OpenEEC-Project/EECSucka-Archive/Sucka/EEC Sucka/esk_bot2.jpg

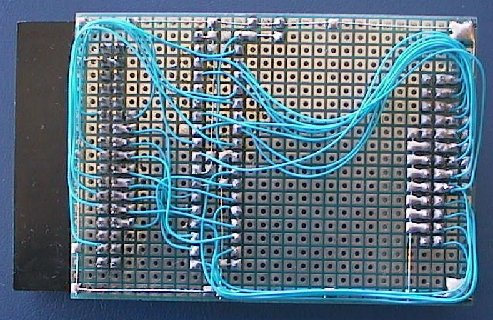
Sucka/EEC Sucka/esk_bot2.jpg
