OpenEEC-Project/EECSucka-Archive/Sucka/EEC Sucka/esk_top2.jpg

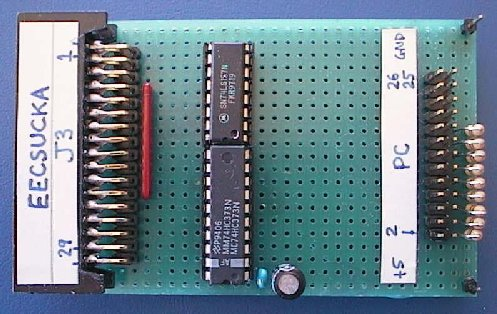
Sucka/EEC Sucka/esk_top2.jpg
