OpenEEC-Project/EECSucka-Archive/Sucka/EZTag/EZTag.bmp

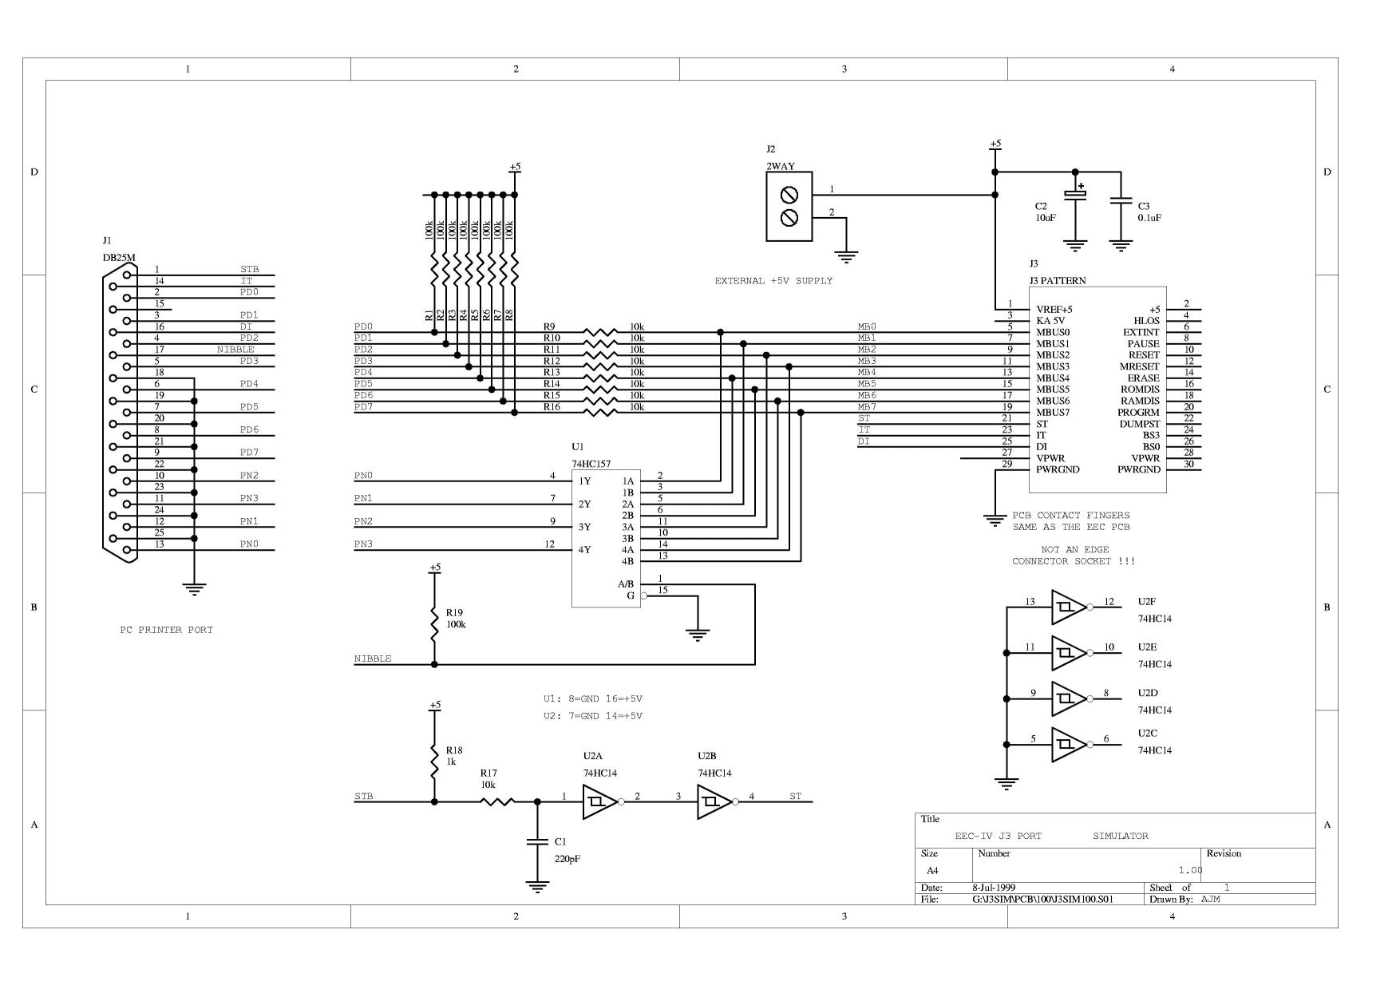
Sucka/EZTag/EZTag.bmp
