OpenEEC-Project/EECSucka-Archive/Sucka/J3 adapter/ea100b_2.jpg

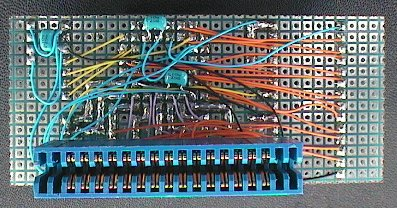
Sucka/J3 adapter/ea100b_2.jpg
