OpenEEC-Project/EECSucka-Archive/Sucka/J3 adapter/ea100w_2.gif

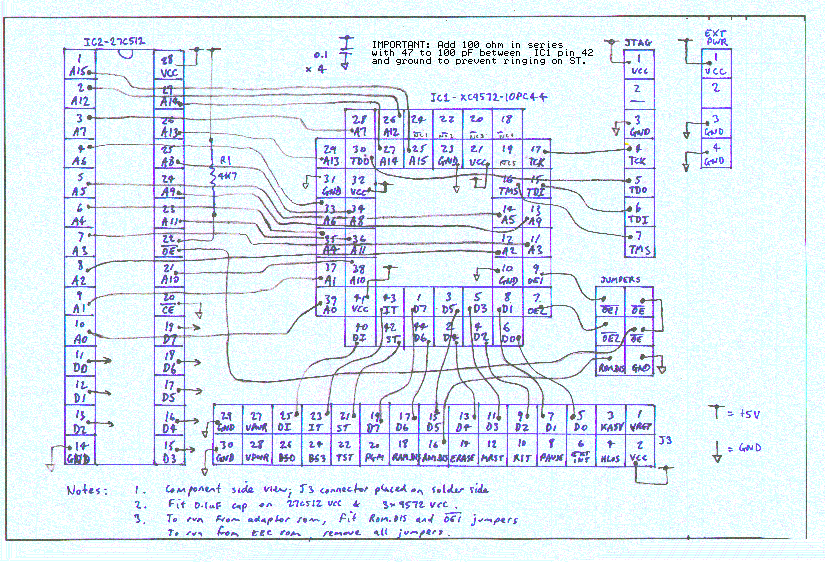
Sucka/J3 adapter/ea100w_2.gif
