OpenEEC-Project/EECSucka-Archive/Sucka/J3 adapter/j3_2.gif

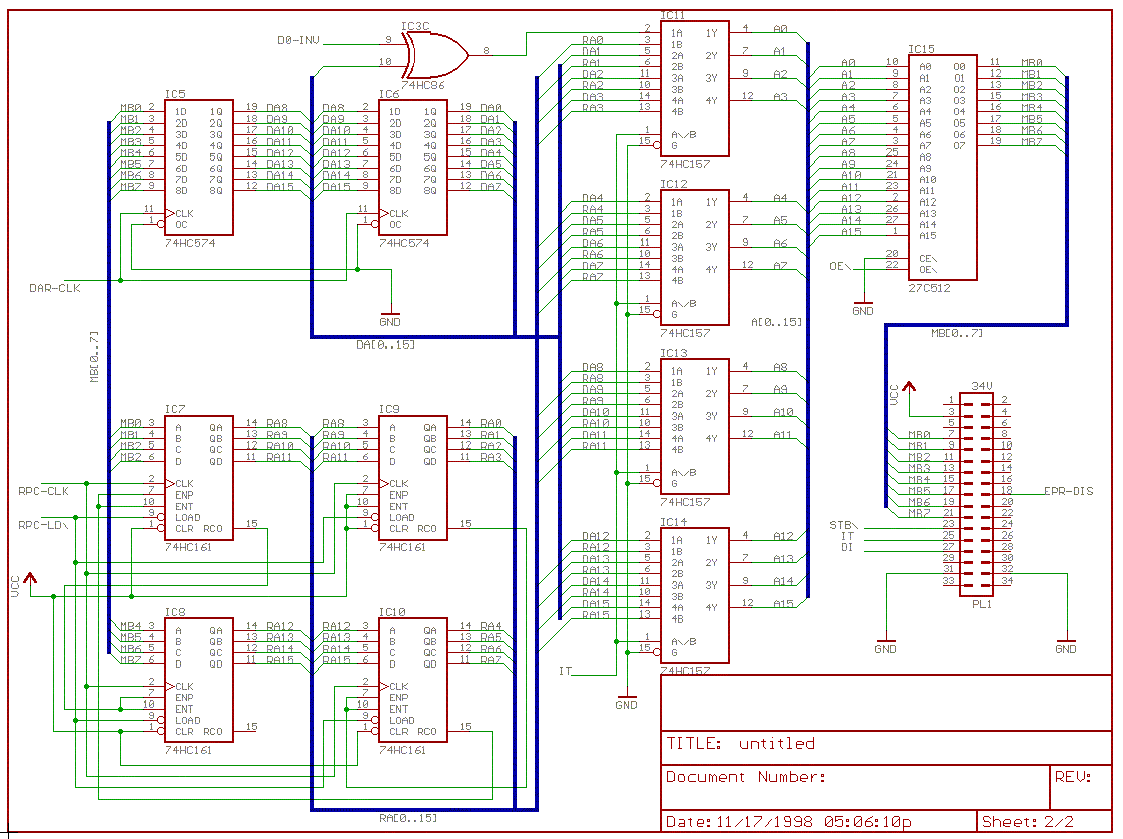
Sucka/J3 adapter/j3_2.gif
