OpenEEC-Project/EECSucka-Archive/Sucka/J3 adapter/sd20e9d1.jpg

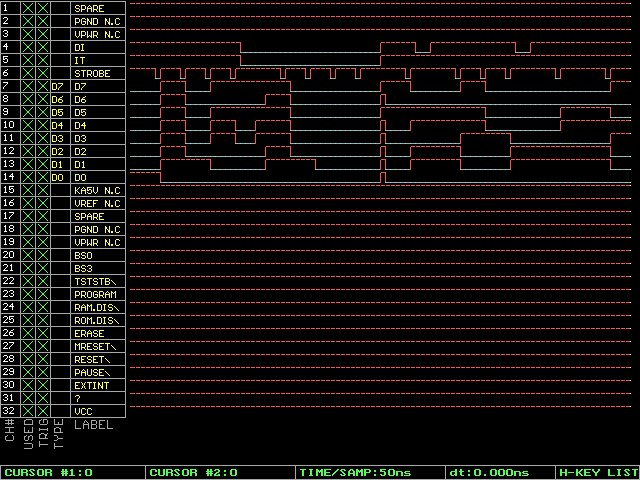
Sucka/J3 adapter/sd20e9d1.jpg
